ForlingTec/STLINK_JLINK_DAPLINK_Debugger/document/固件下载/JLINK升级App固件.jpg

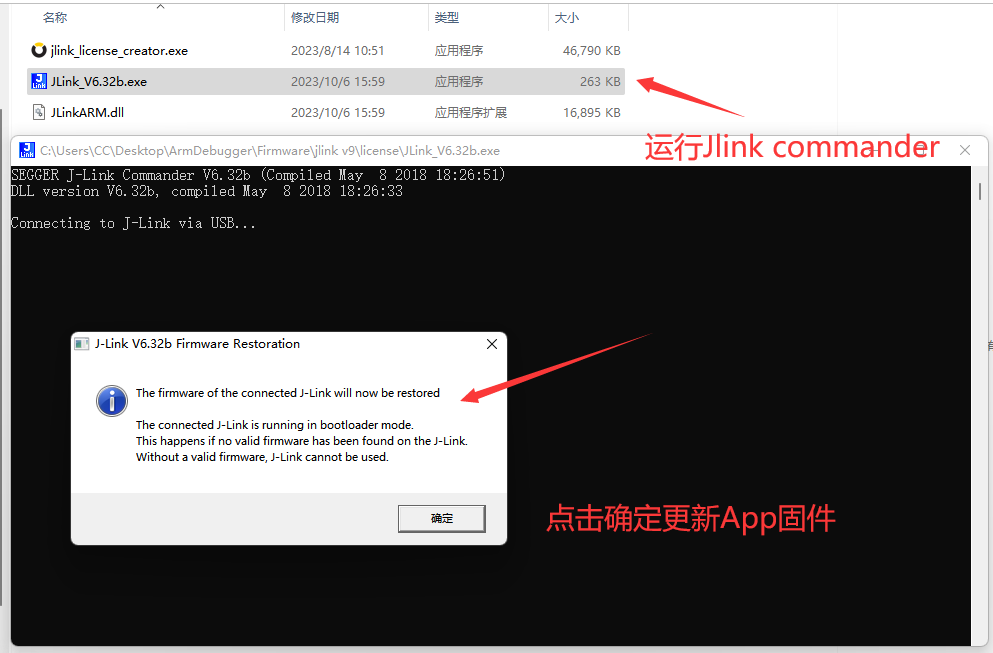
document/固件下载/JLINK升级App固件.jpg
